smores56/sephirette/art/sephirette-silk.png

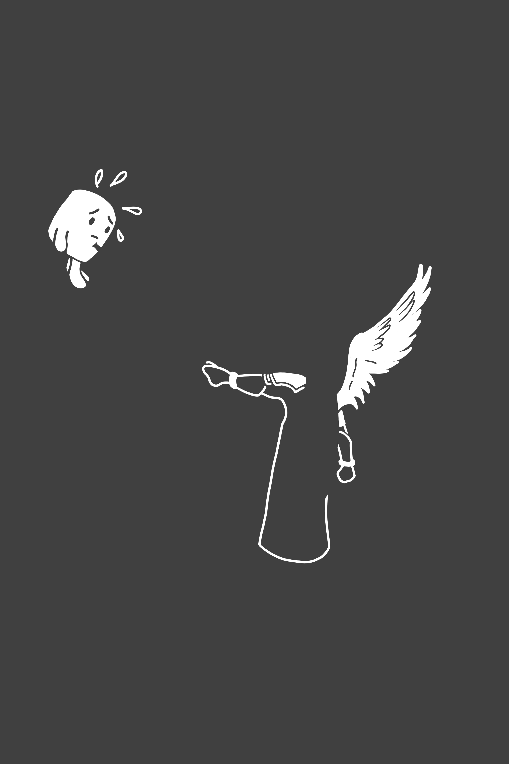
art/sephirette-silk.png
