smores56/sephirette/art/sephirette-title.png

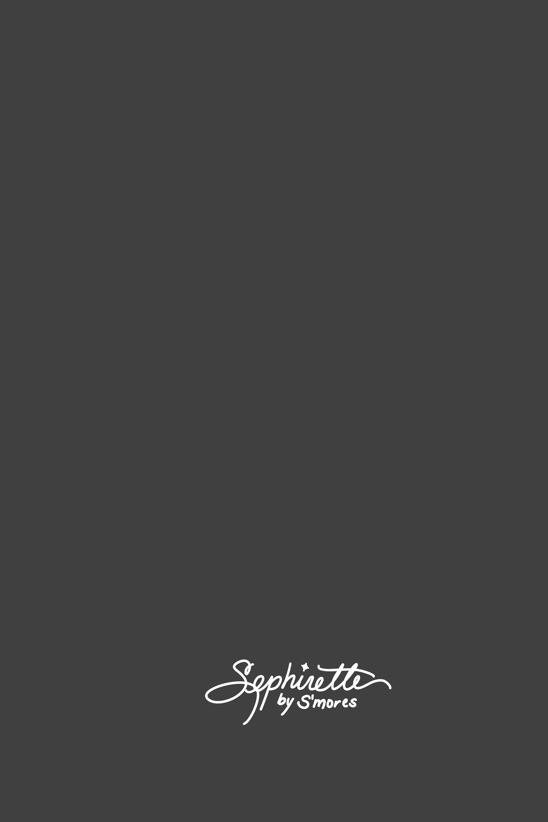
art/sephirette-title.png
